maholli/lora2040/micropython_build/LORA2040/mpconfigboard.h

#define MICROPY_HW_BOARD_NAME          "LORA2040 v00a"
#define MICROPY_HW_FLASH_STORAGE_BYTES (128 * 1024)

#define MICROPY_HW_USB_VID (0x04D8)
#define MICROPY_HW_USB_PID (0xEC44)

#define MICROPY_PY_FRAMEBUF                     (0)
#define MICROPY_PY_SOCKET                       (0)
#define MICROPY_PY_NETWORK                      (0)
